GeorgeIoak/Ikea_Environmental_Sensor/Reference/nRF24L01P-EK/Firmware/nRF24L01_Firmware/nRF_API.c

/** @file API.c
 *
 * @author Runar Kjellhaug
 *
 * @compiler This program has been tested with Keil C51 V7.50.
 *
 *
 * $Date: 20.02.06 14:16 $
 * $Revision: 21 $
 *
 */
#include <cygnal\c8051F320.h>
#include "include\nRF_API.h"
#include "include\LL_API.h"

//**********************************************************//

//**********************************************************//


// Declare HW/SW SPI Mode variable
extern BYTE SPI_Mode;


// Variable that indicates nRF24L01 interrupt source
extern BYTE IRQ_Source;
//********************************************************************************************************************//



//**********************************************************//
//
//  Function: SPI_RW
//
//  Description:
//  Writes one byte to nRF24L01, and return the byte read
//  from nRF24L01 during write, according to SPI protocol
//
//  In/Out parameters:
//  In: 'byte', current byte to be written
//  Out: 'SPI0DAT', HW SPI mode, 'byte' SW SPI mode,
//
//  Author: RSK   Date: 28.11.05
//**********************************************************//
BYTE SPI_RW(BYTE byte)
{
BYTE bit_ctr;
  if (SPI_Mode == HW_MODE)                        // Select HW or SW SPI..
  {
    return(SPI_HW(byte));                         // Perform HW SPI operation
  }
  else                                            // software SPI....
  {
    for(bit_ctr=0;bit_ctr<8;bit_ctr++)
    {
      MOSI_Pin(byte & 0x80);                      // output 'byte', MSB to MOSI
      byte = (byte << 1);                         // shift next bit into MSB..
      SCK_Pin(1);                                 // Set SCK high..
      byte |= MISO_Pin();                         // capture current MISO bit
      SCK_Pin(0);                                 // ..then set SCK low again
    }
    MOSI_Pin(0);                                  // MOSI pin low before return

    return(byte);                                 // return 'read' byte
  }
}


//**********************************************************//
//
//  Function: SPI_Read
//
//  Description:
//  Read one byte from nRF24L01 register, 'reg'
//
//
//  In/Out parameters:
//  In: reg, register to read
//  Out: return reg_val, register value.
//
//
//  Author: RSK   Date: 28.11.05
//**********************************************************//
BYTE SPI_Read(BYTE reg)
{
BYTE reg_val;

  CSN = 0;                                        // CSN low, initialize SPI communication...
  CSN_Pin(0);
  SPI_RW(reg);                                    // Select register to read from..
  reg_val = SPI_RW(0);                            // ..then read registervalue
  CSN_Pin(1);                                     // CSN high, terminate SPI communication

  return(reg_val);                                // return register value
}


//**********************************************************//
//
//  Function: SPI_RW_Reg
//
//  Description:
//  Writes value 'value' to register 'reg'
//
//
//  In/Out parameters:
//  In: 'reg' register to write value 'value' to.
//  Return status byte.
//
//  Author: RSK   Date: 28.11.05
//**********************************************************//
BYTE SPI_RW_Reg(BYTE reg, BYTE value)
{
BYTE status;

  CSN_Pin(0);                                     // CSN low, init SPI transaction
  status = SPI_RW(reg);                           // select register
  SPI_RW(value);                                  // ..and write value to it..
  CSN_Pin(1);                                     // CSN high again

  return(status);                                 // return nRF24L01 status byte
}


//**********************************************************//
//
//  Function: SPI_Write_Buf
//
//  Description:
//  Writes contents of buffer '*pBuf' to nRF24L01
//  Typically used to write TX payload, Rx/Tx address
//
//
//  In/Out parameters:
//  In: register 'reg' to write, buffer '*pBuf*' contains
//  data to be written and buffer size 'buf_size' is #of
//  bytes to be written
//  Out: return nRF24L01 status byte.
//
//  Author: RSK   Date: 28.11.05
//**********************************************************//
BYTE SPI_Write_Buf(BYTE reg, BYTE *pBuf, BYTE bytes)
{
BYTE status,byte_ctr;

  CSN_Pin(0);                                     // Set CSN low, init SPI tranaction
  status = SPI_RW(reg);                           // Select register to write to and read status byte

  for(byte_ctr=0; byte_ctr<bytes; byte_ctr++)     // then write all byte in buffer(*pBuf)
    SPI_RW(*pBuf++);

  CSN_Pin(1);                                     // Set CSN high again

  return(status);                                 // return nRF24L01 status byte
}


//**********************************************************//
//
//  Function: SPI_Read_Buf
//
//  Description:
//  Reads 'bytes' #of bytes from register 'reg'
//  Typically used to read RX payload, Rx/Tx address
//
//
//  In/Out parameters:
//  In: 'reg', register to read from, '*pBuf' are buffer
//  the read bytes are stored to and 'bytes' are #of bytes
//  to read.
//  Out: return nRF24L01 status byte.
//
//  Author: RSK   Date: 28.11.05
//**********************************************************//
BYTE SPI_Read_Buf(BYTE reg, BYTE *pBuf, BYTE bytes)
{
BYTE status,byte_ctr;

  CSN_Pin(0);                                     // Set CSN low, init SPI tranaction
  status = SPI_RW(reg);                           // Select register to write to and read status byte

  for(byte_ctr=0;byte_ctr<bytes;byte_ctr++)
    pBuf[byte_ctr] = SPI_RW(0);                   // Perform SPI_RW to read byte from nRF24L01

  CSN_Pin(1);                                     // Set CSN high again

  return(status);                                 // return nRF24L01 status byte
}

/*

//**********************************************************
//
//  nRF24L01 Program example
//
//  Description:
//  This example code is contains two functions,
//  'TX_Mode': program nRF24L01 to function as a PRIM:TX,
//  i.e. program TX_Address, RX_Address for auto ack,
//  TX Payload, setup of 'Auto Retransmit Delay' &
//  'Auto Retransmit Count', select RF channel,
//  Datarate & RF output power.
//
//  'RX_Mode': program nRF24L01 to function as a PRIM:RX,
//  i.e. ready to receive the packet that was sent with
//  the 'TX_Mode' function.
//
//
//  Author: RSK   Date: 28.11.05
//**********************************************************
#define TX_ADR_LENGTH   5                         // 5 bytes TX(RX) address width
#define TX_PLOAD_WIDTH  16                        // 16 bytes TX payload

// Predefine a static TX address
BYTE const TX_ADDRESS[TX_ADR_LENGTH]  = {0x34,0x43,0x10,0x10,0x01}; 
// Predefine TX payload packet..
BYTE const TX_PAYLOAD[TX_PLOAD_WIDTH] = {0x00,0x01,0x02,0x03,0x04,0x05,0x06,0x07,
                                         0x08,0x09,0x0a,0x0b,0x0c,0x0d,0x0e,0x0f};  

extern BYTE SPI_Buffer[32];                       // Buffer to hold data from 'SPI_Read_Buf()' function

//**********************************************************
//
//  Function: TX_Mode
//
//  Description:
//  This function initializes one nRF24L01 device to
//  TX mode, set TX address, set RX address for auto.ack,
//  fill TX payload, select RF channel, datarate & TX pwr.
//  PWR_UP is set, CRC(2 bytes) is enabled, & PRIM:TX.
//
//  ToDo: One high pulse(>10µs) on CE will now send this
//  packet and expext an acknowledgment from the RX device.
//
//
//  Author: RSK   Date: 28.11.05
//**********************************************************
void TX_Mode(void)
{
  SPI_Write_Buf(WRITE_REG + TX_ADDR, TX_ADDRESS, TX_ADR_LENGTH);    // Writes TX_Address to nRF24L01
  SPI_Write_Buf(WRITE_REG + RX_ADDR_P0, TX_ADDRESS, TX_ADR_LENGTH); // RX_Addr0 same as TX_Adr for Auto.Ack
  SPI_Write_Buf(WR_TX_PLOAD, TX_PAYLOAD, TX_PLOAD_WIDTH); // Writes data to TX payload

  SPI_RW_Reg(WRITE_REG + EN_AA, 0x01);            // Enable Auto.Ack:Pipe0
  SPI_RW_Reg(WRITE_REG + EN_RXADDR, 0x01);        // Enable Pipe0
  SPI_RW_Reg(WRITE_REG + SETUP_RETR, 0x1a);       // 500µs + 86µs, 10 retrans...
  SPI_RW_Reg(WRITE_REG + RF_CH, 40);              // Select RF channel 40
  SPI_RW_Reg(WRITE_REG + RF_SETUP, 0x0f);         // TX_PWR:0dBm, Datarate:2Mbps, LNA:HCURR
  SPI_RW_Reg(WRITE_REG + CONFIG, 0x0e);           // Set PWR_UP bit, enable CRC(2 bytes) & Prim:TX. MAX_RT & TX_DS enabled..

  //  This device is now ready to transmit one packet of 16 bytes payload to a RX device at address
  //  '3443101001', with auto acknowledgment, retransmit count of 10(retransmit delay of 500µs+86µs)
  //  RF channel 40, datarate = 2Mbps with TX power = 0dBm.
}


//**********************************************************
//
//  Function: RX_Mode
//
//  Description:
//  This function initializes one nRF24L01 device to
//  RX Mode, set RX address, writes RX payload width,
//  select RF channel, datarate & LNA HCURR.
//  After init, CE is toggled high, which means that
//  this device is now ready to receive a datapacket.
//
//  Author: RSK   Date: 28.11.05
//**********************************************************
void RX_Mode(void)
{
  SPI_Write_Buf(WRITE_REG + RX_ADDR_P0, TX_ADDRESS, TX_ADR_LENGTH); // Use the same address on the RX device as the TX device

  SPI_RW_Reg(WRITE_REG + EN_AA, 0x01);            // Enable Auto.Ack:Pipe0
  SPI_RW_Reg(WRITE_REG + EN_RXADDR, 0x01);        // Enable Pipe0
  SPI_RW_Reg(WRITE_REG + RF_CH, 40);              // Select RF channel 40
  SPI_RW_Reg(WRITE_REG + RX_PW_P0, TX_PLOAD_WIDTH); // Select same RX payload width as TX Payload width
  SPI_RW_Reg(WRITE_REG + RF_SETUP, 0x0f);         // TX_PWR:0dBm, Datarate:2Mbps, LNA:HCURR
  SPI_RW_Reg(WRITE_REG + CONFIG, 0x0f);           // Set PWR_UP bit, enable CRC(2 bytes) & Prim:RX. RX_DR enabled..

  CE = 1; // Set CE pin high to enable RX device

  //  This device is now ready to receive one packet of 16 bytes payload from a TX device sending to address
  //  '3443101001', with auto acknowledgment, retransmit count of 10, RF channel 40 and datarate = 2Mbps.

}

void nRF24L01_IRQ(void) interrupt EXT_INT0
{
BYTE temp,rx_pw;

  EA = 0; // disable global interrupt during processing
  temp = SPI_RW_Reg(WRITE_REG + STATUS, 0x70);    // Read STATUS byte and clear IRQ flag's(nRF24L01)

  if(temp & MAX_RT) IRQ_Source = MAX_RT;          // Indicates max #of retransmit interrupt
  if(temp & TX_DS)  IRQ_Source = TX_DS;           // Indicates TX data succsessfully sent

  if(temp & RX_DR)  // In RX mode, check for data received
  {
    // Data received, so find out which datapipe the data was received on:
    temp = (0x07 & (temp > 1)); // Shift bits in status byte one bit to LSB and mask 'Data Pipe Number'
    rx_pw = SPI_Read(READ_REG + RX_PW_P0 + temp); // Read current RX_PW_Pn register, where Pn is the pipe the data was received on..
    SPI_Read_Buf(RD_RX_PLOAD, SPI_Buffer, rx_pw); // Data from RX Payload register is now copied to SPI_Buffer[].

    IRQ_Source = RX_DR; // Indicates RX data received
  }
  EA = 1; // enable global interrupt again
}
*/
